CrazyRobMiles/custard-cream-camera/assets/images/watermark master.png

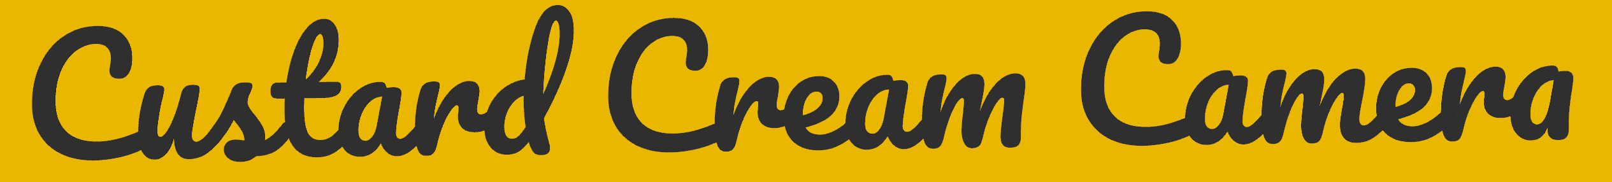
assets/images/watermark master.png
