CrazyRobMiles/custard-cream-camera/case/BatteryLidLeft.stl

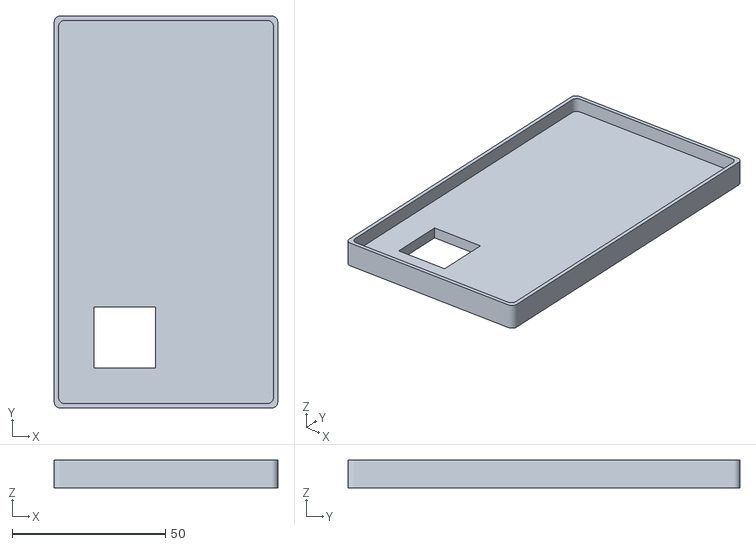
[picture p18: CAD file, 2026-08-17]
case/BatteryLidLeft.stl
73.0 x 128.0 x 9.00
