CrazyRobMiles/custard-cream-camera/case/PrinterLidRight.stl

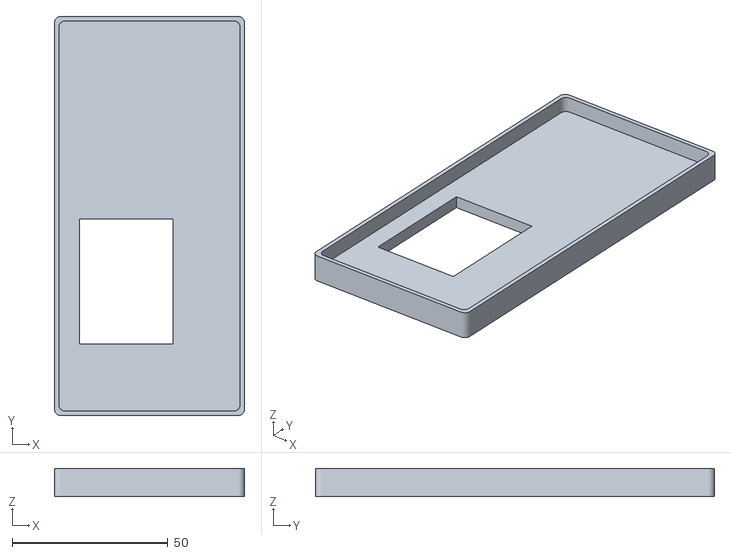
[picture p19: CAD file, 2026-08-17]
case/PrinterLidRight.stl
61.0 x 128.0 x 9.00
